TheThingsIndustries/generic-node-se/Software/target/stm32wlxx_hal_driver/README.md

# STM32CubeWL HAL Driver MCU Component

## Overview

**STM32Cube** is an STMicroelectronics original initiative to ease the developers life by reducing efforts, time and cost.

**STM32Cube** covers the overall STM32 products portfolio. It includes a comprehensive embedded software platform delivered for each STM32 series.
   * The CMSIS modules (core and device) corresponding to the ARM(tm) core implemented in this STM32 product.
   * The STM32 HAL-LL drivers, an abstraction layer offering a set of APIs ensuring maximized portability across the STM32 portfolio.
   * The BSP drivers of each evaluation, demonstration or nucleo board provided for this STM32 series.
   * A consistent set of middleware components such as RTOS, USB, FatFS, graphics, touch sensing library...
   * A full set of software projects (basic examples, applications, and demonstrations) for each board provided for this STM32 series.

Two models of publication are proposed for the STM32Cube embedded software:
   * The monolithic **MCU Package**: all STM32Cube software modules of one STM32 series are present (Drivers, Middleware, Projects, Utilities) in the repository (usual name **STM32Cubexx**, xx corresponding to the STM32 series).
   * The **MCU component**: each STM32Cube software module being part of the STM32Cube MCU Package, is delivered as an individual repository, allowing the user to select and get only the required software functions.

## Description

This **stm32wlxx_hal_driver** MCU component repo is one element of the STM32CubeWL MCU embedded software package, providing the **HAL-LL Drivers** part.

## License

Copyright (c) 2020 STMicroelectronics.

This software component is licensed by STMicroelectronics under BSD-3-Clause license. You may not use this software except in compliance with the License. 
You may obtain a copy of the License [here](https://opensource.org/licenses/BSD-3-Clause).

## Release note

Details about the content of this release are available in the release note [here](https://htmlpreview.github.io/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).

## Compatibility information

In this table, you can find the successive versions of this HAL-LL Driver component, in line with the corresponding versions of the full MCU package.

It is **crucial** that you use a consistent set of versions for the CMSIS Core - CMSIS Device - HAL, as mentioned in this table.

HAL Driver WL | CMSIS Device WL | CMSIS Core | Was delivered in the full MCU package
------------- | --------------- | ---------- | -------------------------------------
Tag v1.0.0 | Tag v1.0.0 | Tag V5.6.0_cm4 | Tag v1.0.0 (and following, if any, till next HAL tag)

The full **STM32CubeWL** MCU package is available [here](https://github.com/STMicroelectronics/STM32CubeWL).

## Troubleshooting

If you have any issue with the **software content** of this repository, you can file an issue [here](https://github.com/STMicroelectronics/stm32wlxx_hal_driver/issues/new/choose).

For any other question related to the product, the tools, the environment, you can submit a topic to the [ST Community](https://community.st.com/s/).
