TheThingsIndustries/generic-node-se/Software/app/sensors_lorawan_se/stm32wlxx_it.c

/**
  ******************************************************************************
  * @file    stm32wlxx_it.c
  * @brief   Interrupt Service Routines.
  ******************************************************************************
  * @attention
  *
  * <h2><center>&copy; Copyright (c) 2020 STMicroelectronics.
  * All rights reserved.</center></h2>
  *
  * This software component is licensed by ST under Ultimate Liberty license
  * SLA0044, the "License"; You may not use this file except in compliance with
  * the License. You may obtain a copy of the License at:
  *                             www.st.com/SLA0044
  *
  ******************************************************************************
  */

#include "GNSE_bsp.h"
#include "stm32wlxx_it.h"

extern RTC_HandleTypeDef hrtc;
extern SUBGHZ_HandleTypeDef hsubghz;

/******************************************************************************/
/*           Cortex Processor Interruption and Exception Handlers          */
/******************************************************************************/
/**
  * @brief This function handles Non maskable interrupt.
  */
void NMI_Handler(void)
{
}

/**
  * @brief This function handles Hard fault interrupt.
  */
void HardFault_Handler(void)
{
  while (1)
  {
  }
}

/**
  * @brief This function handles Memory management fault.
  */
void MemManage_Handler(void)
{
  while (1)
  {
  }
}

/**
  * @brief This function handles Prefetch fault, memory access fault.
  */
void BusFault_Handler(void)
{
  while (1)
  {
  }
}

/**
  * @brief This function handles Undefined instruction or illegal state.
  */
void UsageFault_Handler(void)
{
  while (1)
  {
  }
}

/**
  * @brief This function handles System service call via SWI instruction.
  */
void SVC_Handler(void)
{
}

/**
  * @brief This function handles Debug monitor.
  */
void DebugMon_Handler(void)
{
}

/**
  * @brief This function handles Pendable request for system service.
  */
void PendSV_Handler(void)
{
}

/**
  * @brief This function handles System tick timer.
  */
void SysTick_Handler(void)
{
  HAL_IncTick();
}

/**
  * @brief This function handles RTC Tamper, RTC TimeStamp, LSECSS and RTC SSRU Interrupts.
  */
void TAMP_STAMP_LSECSS_SSRU_IRQHandler(void)
{
  HAL_RTCEx_SSRUIRQHandler(&GNSE_BSP_rtc);
}

/**
  * @brief This function handles EXTI Line 0 Interrupt.
  */
void EXTI0_IRQHandler(void)
{
  HAL_GPIO_EXTI_IRQHandler(GPIO_PIN_0);
}

/**
  * @brief This function handles EXTI Line 1 Interrupt.
  */
void EXTI1_IRQHandler(void)
{
  HAL_GPIO_EXTI_IRQHandler(GPIO_PIN_1);
}

/**
  * @brief This function handles EXTI Line 3 Interrupt.
  */
void EXTI3_IRQHandler(void)
{
  HAL_GPIO_EXTI_IRQHandler(GPIO_PIN_3);
}

void USART2_IRQHandler(void)
{
  HAL_UART_IRQHandler(&GNSE_BSP_debug_usart);
}

void DMA1_Channel5_IRQHandler(void)
{
  HAL_DMA_IRQHandler(&GNSE_BSP_hdma_tx);
}

/**
  * @brief This function handles RTC Alarms (A and B) Interrupt.
  */
void RTC_Alarm_IRQHandler(void)
{
  HAL_RTC_AlarmIRQHandler(&GNSE_BSP_rtc);
}

/**
  * @brief This function handles SUBGHZ Radio Interrupt.
  */
void SUBGHZ_Radio_IRQHandler(void)
{
  HAL_SUBGHZ_IRQHandler(&hsubghz);
}

/************************ (C) COPYRIGHT STMicroelectronics *****END OF FILE****/
