TheThingsIndustries/generic-node-se/Software/app/sensors_lorawan_se/stm32wlxx_it.h

/**
  ******************************************************************************
  * @file    stm32wlxx_it.h
  * @brief   This file contains the headers of the interrupt handlers.
  ******************************************************************************
  * @attention
  *
  * <h2><center>&copy; Copyright (c) 2020 STMicroelectronics.
  * All rights reserved.</center></h2>
  *
  * This software component is licensed by ST under Ultimate Liberty license
  * SLA0044, the "License"; You may not use this file except in compliance with
  * the License. You may obtain a copy of the License at:
  *                             www.st.com/SLA0044
  *
 ******************************************************************************
  */

#ifndef __STM32WLxx_IT_H
#define __STM32WLxx_IT_H

#ifdef __cplusplus
 extern "C" {
#endif

void NMI_Handler(void);
void HardFault_Handler(void);
void MemManage_Handler(void);
void BusFault_Handler(void);
void UsageFault_Handler(void);
void SVC_Handler(void);
void DebugMon_Handler(void);
void PendSV_Handler(void);
void SysTick_Handler(void);
void TAMP_STAMP_LSECSS_SSRU_IRQHandler(void);
void EXTI0_IRQHandler(void);
void EXTI1_IRQHandler(void);
void EXTI3_IRQHandler(void);
void DMA1_Channel5_IRQHandler(void);
void USART2_IRQHandler(void);
void RTC_Alarm_IRQHandler(void);
void SUBGHZ_Radio_IRQHandler(void);

#ifdef __cplusplus
}
#endif

#endif /* __STM32WLxx_IT_H */

/************************ (C) COPYRIGHT STMicroelectronics *****END OF FILE****/
